Jacquot-SFE/TeensyBoom/TeensyBoomVoiceLibrary/TeensyBoomVoiceLibrary.h

#ifndef __TEENSY_BOOM_VOICE_LIBRARY_H_
#define __TEENSY_BOOM_VOICE_LIBRARY_H_

#pragma once

#include <Audio.h>

#include "synth_simple_drum.h"
#include "Synth-Clatter.h"
#include "Synth-Decay.h"
#include "Synth-DrumHeart.h"
#include "Effect-ClapEnv.h"

#endif
