Jacquot-SFE/TeensyBoom/TeensyBoom/panel-scanner.cpp

#include <SPI.h>
#include <arduino.h>

#include "panel-scanner.h"
#include "player.h"

static const int32_t CHIPSEL_BTNS = 8;
static const int32_t CHIPSEL_LEDS = 5;

extern Editor       theEditor;
extern Player       thePlayer;

static const SPISettings registersettings(1000000, MSBFIRST, SPI_MODE0 );


// constructor...
PanelScanner::PanelScanner()
{
  for (uint32_t i = 0; i < NUM_PANELS; i++)
  {
    led_half_buffer[i] = 0;
    led_background_buffer[i] = 0;
    led_blinking_buffer[i] = 0;
    led_overlay_buffer[i] = 0;
    old_buttons[i] = 0;
    new_buttons[i] = 0;
  }

}

void PanelScanner::initScanning()
{
  //  SPI is shared with SD card, initialized in setup()
  //  SPI.setSCK(14);
  //  SPI.setMOSI(7);
  //  SPI.begin();

  pinMode(CHIPSEL_BTNS, OUTPUT);
  digitalWrite(CHIPSEL_BTNS, LOW);
  pinMode(CHIPSEL_LEDS, OUTPUT);
  digitalWrite(CHIPSEL_LEDS, LOW);

}

void PanelScanner::tick()
{
  doTransaction();
  parseButtons();
}


void PanelScanner::clearAllLED()
{
  for (uint32_t i = 0; i < NUM_PANELS; i++)
  {
    led_half_buffer[i] = 0;
    led_background_buffer[i] = 0;
    led_blinking_buffer[i] = 0;
    led_overlay_buffer[i] = 0;
  }
}


void PanelScanner::setHalfLED(uint32_t num, bool on)
{
  uint32_t byte_idx, bit_num;

#if 0
  Serial.print("set half: ");
  Serial.print(num);
  Serial.print(" ");
  Serial.println(on);
#endif

  if (!on)
  {
    clearHalfLED(num);
    return;
  }

  // Funny math at play here.
  // LEDs are out of order WRT the buttons...the first bit shifted in is the
  // last bit shifted out on the SPI ring.
  // So we'll flop that around here by doing the shifting and indexing
  // math from the top down, rather than bottom up.

  if (num < (NUM_PANELS * 8))
  {
    byte_idx = NUM_PANELS - 1 - (num / 8);
    bit_num = num % 8;

    led_half_buffer[byte_idx] |= 0x80 >> bit_num;
  }
}

void PanelScanner::clearHalfLED(uint32_t num)
{
  uint32_t byte_idx, bit_num;

  // see note above.

  if (num < (NUM_PANELS * 8))
  {
    byte_idx = NUM_PANELS - 1 - (num / 8);
    bit_num = num % 8;

    led_half_buffer[byte_idx] &= ~(0x80 >> bit_num);
  }
}

void PanelScanner::clearAllHalfLEDs()
{
  for (uint32_t i = 0; i < NUM_PANELS; i++)
  {
    led_half_buffer[i] = 0;
  }
}



void PanelScanner::setBackgroundLED(uint32_t num, bool on)
{
  uint32_t byte_idx, bit_num;

#if 0
  Serial.print("set background: ");
  Serial.print(num);
  Serial.print(" ");
  Serial.println(on);
#endif

  if (!on)
  {
    clearBackgroundLED(num);
    return;
  }

  // Funny math at play here.
  // LEDs are out of order WRT the buttons...the first bit shifted in is the
  // last bit shifted out on the SPI ring.
  // So we'll flop that around here by doing the shifting and indexing
  // math from the top down, rather than bottom up.

  if (num < (NUM_PANELS * 8))
  {
    byte_idx = NUM_PANELS - 1 - (num / 8);
    bit_num = num % 8;

    led_background_buffer[byte_idx] |= 0x80 >> bit_num;
  }
}

void PanelScanner::clearBackgroundLED(uint32_t num)
{
  uint32_t byte_idx, bit_num;

  // see note above.

  if (num < (NUM_PANELS * 8))
  {
    byte_idx = NUM_PANELS - 1 - (num / 8);
    bit_num = num % 8;

    led_background_buffer[byte_idx] &= ~(0x80 >> bit_num);
  }
}

void PanelScanner::clearAllBackgroundLEDs()
{
  for (uint32_t i = 0; i < NUM_PANELS; i++)
  {
    led_background_buffer[i] = 0;
  }
}

//////////////////////////////////////////////
void PanelScanner::setBlinkingLED(uint32_t num, bool on)
{
  uint32_t byte_idx, bit_num;

#if 0
  Serial.print("set blinking: ");
  Serial.println(num);
#endif

  if (!on)
  {
    clearBlinkingLED(num);
    return;
  }

  // Funny math at play here.
  // LEDs are out of order WRT the buttons...the first bit shifted in is the
  // last bit shifted out on the SPI ring.
  // So we'll flop that around here by doing the shifting and indexing
  // math from the top down, rather than bottom up.

  if (num < (NUM_PANELS * 8))
  {
    byte_idx = NUM_PANELS - 1 - (num / 8);
    bit_num = num % 8;

    led_blinking_buffer[byte_idx] |= 0x80 >> bit_num;
  }
}

void PanelScanner::clearBlinkingLED(uint32_t num)
{
  uint32_t byte_idx, bit_num;

  // see note above.

  if (num < (NUM_PANELS * 8))
  {
    byte_idx = NUM_PANELS - 1 - (num / 8);
    bit_num = num % 8;

    led_blinking_buffer[byte_idx] &= ~(0x80 >> bit_num);
  }
}

void PanelScanner::clearAllBlinkingLEDs()
{
#if 0
  Serial.println("Clear all blinking");
#endif
  for (uint32_t i = 0; i < NUM_PANELS; i++)
  {
    led_blinking_buffer[i] = 0;
  }
}
///////////////////////////////////

void PanelScanner::setOverlayLED(uint32_t num)
{
  uint32_t byte_idx, bit_num;

#if 0
  Serial.print("OL on #");
  Serial.println(num);
#endif

  // Funny math at play here.
  // LEDs are out of order WRT the buttons...the first bit shifted in is the
  // last bit shifted out on the SPI ring.
  // So we'll flop that around here by doing the shifting and indexing
  // math from the top down, rather than bottom up.

  if (num < (NUM_PANELS * 8))
  {
    byte_idx = NUM_PANELS - 1 - (num / 8);
    bit_num = num % 8;

    led_overlay_buffer[byte_idx] |= 0x80 >> bit_num;
  }
}

void PanelScanner::clearOverlayLED(uint32_t num)
{
  uint32_t byte_idx, bit_num;

  // see note above.

  if (num < (NUM_PANELS * 8))
  {
    byte_idx = NUM_PANELS - 1 - (num / 8);
    bit_num = num % 8;

    led_overlay_buffer[byte_idx] &= ~(0x80 >> bit_num);
  }
}

void PanelScanner::clearAllOverlayLEDs()
{
  for (uint32_t i = 0; i < NUM_PANELS; i++)
  {
    led_overlay_buffer[i] = 0;
  }

}


void PanelScanner::parseButtons()
{
  uint8_t diff;

  for (uint32_t i = 0; i < NUM_PANELS; i++)
  {
    // in each byte, see if anything changed from last invocation
    diff = new_buttons[i] ^ old_buttons[i];

    for (uint32_t j = 0, mask = 0x01; j < 8; j++, mask <<= 1)
    {
      if (diff & mask)
      {
        //Serial.println(new_buttons[i]);
        theEditor.receiveKey((i * 8) + j, (new_buttons[i] & mask));
      }
    }

    // then store the new state for comparison next time
    old_buttons[i] = new_buttons[i];
  }
}

void PanelScanner::dumpLEDs()
{
  Serial.print(led_background_buffer[0], HEX);
  Serial.print(led_background_buffer[1], HEX);
  Serial.println(led_background_buffer[2], HEX);

  Serial.print(led_blinking_buffer[0], HEX);
  Serial.print(led_blinking_buffer[1], HEX);
  Serial.println(led_blinking_buffer[2], HEX);

  Serial.print(led_overlay_buffer[0], HEX);
  Serial.print(led_overlay_buffer[1], HEX);
  Serial.println(led_overlay_buffer[2], HEX);
}


void PanelScanner::doTransaction()
{
  uint32_t i;
  //static uint32_t count = 0;
  uint8_t trans_buffer[NUM_PANELS];

  //count++;

  // Ask the player for 1/32 step info for sync'd blinking
  bool blink_phase = thePlayer.getBlinkPhase();

  for (i = 0; i < NUM_PANELS; i++)
  {
    if (blink_phase)
    {
      trans_buffer[i] = led_half_buffer[i];
    }
    else
    {
      trans_buffer[i] = 0;
    }

    trans_buffer[i] |= led_background_buffer[i];
    trans_buffer[i] ^= led_overlay_buffer[i];

    // Blinking supersedes static state...if blinking, it should blink,
    // regardless of underlying static setting.
    if (blink_phase)
    {
      trans_buffer[i] |= led_blinking_buffer[i];
    }
    else
    {
      trans_buffer[i] &= ~led_blinking_buffer[i];

    }
  }

  SPI.beginTransaction(registersettings);

  digitalWrite(CHIPSEL_BTNS, HIGH);

  SPI.transfer(trans_buffer, NUM_PANELS);

  digitalWrite(CHIPSEL_LEDS, HIGH);
  digitalWrite(CHIPSEL_BTNS, LOW);
  digitalWrite(CHIPSEL_LEDS, LOW);

  SPI.endTransaction();


  for (i = 0; i < NUM_PANELS; i++)
  {
    // Button lines are pulled high by resistors, shorted
    // to ground when button is pressed.
    // Invert what we read to make active high
    new_buttons[i] = ~trans_buffer[i];
  }
}
